scrapcomputing/MCEBlaster/firmware/src/Bitmaps.h

//-*- C++ -*-
//
// Copyright (C) 2024 Scarp Computing
//

// clang-format off

#ifndef __BITMAPS_H__
#define __BITMAPS_H__

#include <cstdint>

static constexpr const int BMapWidth = 8;
static constexpr const int BMapHeight = 8;

static constexpr const uint8_t Char_0[] {
  0b00000000,
  0b00111100,
  0b01100110,
  0b01100110,
  0b01100110,
  0b01100110,
  0b00111100,
  0b00000000,
};

static constexpr const uint8_t Char_1[] {
  0b00000000,
  0b00011000,
  0b00111000,
  0b00011000,
  0b00011000,
  0b00011000,
  0b00011000,
  0b00000000,
};

static constexpr const uint8_t Char_2[] {
  0b00000000,
  0b00111100,
  0b01100110,
  0b00001100,
  0b00011000,
  0b00110000,
  0b01111110,
  0b00000000,
};

static constexpr const uint8_t Char_3[] {
  0b00000000,
  0b00111100,
  0b01100110,
  0b00000110,
  0b00011100,
  0b01100110,
  0b00111100,
  0b00000000,
};

static constexpr const uint8_t Char_4[] {
  0b00000000,
  0b00001100,
  0b00011100,
  0b00101100,
  0b00101100,
  0b01111110,
  0b00001100,
  0b00000000,
};

static constexpr const uint8_t Char_5[] {
  0b00000000,
  0b01111110,
  0b01100000,
  0b01100000,
  0b01111100,
  0b00000110,
  0b01111100,
  0b00000000,
};

static constexpr const uint8_t Char_6[] {
  0b00000000,
  0b00111000,
  0b01100000,
  0b01100000,
  0b01111100,
  0b01100110,
  0b00111100,
  0b00000000,
};

static constexpr const uint8_t Char_7[] {
  0b00000000,
  0b01111110,
  0b01100110,
  0b00001100,
  0b00011000,
  0b00110000,
  0b00110000,
  0b00000000,
};

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
  0b01000000,
  0b01000000,
  0b01000000,
  0b01111110,
  0b00000000,
};

static constexpr const uint8_t Char_SQBR_CLOSE[] {
  0b00000000,
  0b01111110,
  0b00000010,
  0b00000010,
  0b00000010,
  0b00000010,
  0b01111110,
  0b00000000,
};


// clang-format on

#endif // __BITMAPS_H__
