scrapcomputing/MCEBlaster/firmware/src/Pico.cpp

//-*- C++ -*-
//
// Copyright (C) 2024 Scrap Computing
//

#include "Pico.h"
#include "Debug.h"
#include "Utils.h"
#include "config.h"
#include "hardware/pll.h"
#include "hardware/structs/rosc.h"
#include "hardware/structs/scb.h"
#include <iomanip>

PinRange::PinRange(uint32_t From, uint32_t To) : From(From), To(To) {
  Mask = ((1u << (To + 1 - From)) - 1) << From;
}

void PinRange::dump(std::ostream &OS) const {
  auto Flags = OS.flags();
  if (From == To)
    OS << std::setw(5) << std::setfill(' ') << From;
  else
    OS << std::setw(2) << From << "-" << std::setw(2) << To;
  OS << " Mask=";
  OS << "0x" << std::setw(8) << std::setfill('0') << std::hex << Mask;
  OS.flags(Flags);
}

void PinRange::dump() const { dump(std::cerr); }

Pico::Pico() {
  // Some valid frequencies: 225000, 250000, 270000, 280000, 290400
  // Voltages: <pico-sdk>/src/rp2_common/hardware_vreg/include/hardware/vreg.h
  //           Examples:  VREG_VOLTAGE_0_85 0.85v
  //                      VREG_VOLTAGE_1_30 1.30v
  if (PICO_VOLTAGE != PICO_DEFAULT_VOLTAGE)
    vreg_set_voltage(PICO_VOLTAGE);
  // Some over/underclocking if needed.
  if (PICO_FREQ != PICO_DEFAULT_FREQ)
    set_sys_clock_khz(PICO_FREQ, false);

  // Initialize stdio so that we can print debug messages.
  stdio_init_all();
  // Initialize the Pico LED.
#ifndef PICO_WIRELESS
  // pico_w has no LED.
  gpio_init(PICO_DEFAULT_LED_PIN);
  gpio_set_dir(PICO_DEFAULT_LED_PIN, GPIO_OUT);
#endif

  // Wait for a bit otherwise this does not show up during serial debug.
  DBG_PRINT(sleep_ms(1500);)
  std::cerr << "+---------------------------------+\n";
  std::cerr << "|          " << PROJECT_NAME << "\n";
  std::cerr << "+---------------------------------+\n";
  std::cerr << "clk_sys = " << frequency_count_khz(CLOCKS_FC0_SRC_VALUE_CLK_SYS)
            << "KHz\n";
  std::cerr << "clk_usb = " << frequency_count_khz(CLOCKS_FC0_SRC_VALUE_CLK_USB)
            << "KHz\n";
  std::cerr << "clk_peri = "
            << frequency_count_khz(CLOCKS_FC0_SRC_VALUE_CLK_PERI) << "KHz\n";
  std::cerr << "clk_ref = " << frequency_count_khz(CLOCKS_FC0_SRC_VALUE_CLK_REF)
            << "KHz\n";
#ifdef PICO1
  std::cerr << "clk_rtc = " << frequency_count_khz(CLOCKS_FC0_SRC_VALUE_CLK_RTC)
            << "KHz\n";
#endif
#ifdef PICO2
  std::cerr << "clk_adc = " << frequency_count_khz(CLOCKS_FC0_SRC_VALUE_CLK_ADC)
            << "KHz\n";
#endif
}

void Pico::initGPIO(const PinRange &Pins, int Direction, Pull Pull,
                    const char *Descr) {
  DBG_PRINT(std::cout << "Setting up GPIO " << std::setw(5) << std::setfill(' ') << Descr
            << " ";)
  DBG_PRINT(Pins.dump(std::cout);)
  DBG_PRINT(std::cout << " " << (Direction == GPIO_IN ? "IN" : "OUT") << "\n";)
  for (uint32_t Pin = Pins.getFrom(), E = Pins.getTo(); Pin <= E; ++Pin) {
    gpio_init(Pin);
    gpio_set_dir(Pin, Direction);
    switch (Pull) {
    case Pull::Up:
      gpio_pull_up(Pin);
      break;
    case Pull::Down:
      gpio_pull_down(Pin);
      break;
    case Pull::None:
      gpio_disable_pulls(Pin);
      break;
    }
  }
}
